sabotrax/agon-retro-case/pic/presentation/ac15-chamfered_egde.jpg

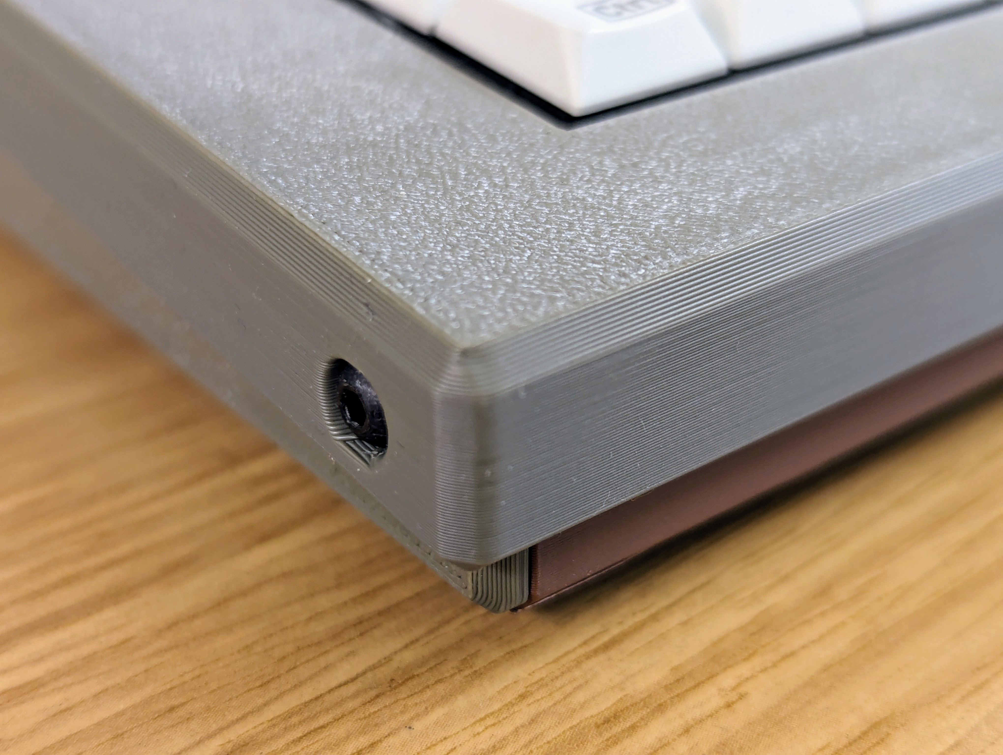
pic/presentation/ac15-chamfered_egde.jpg
