sabotrax/agon-retro-case/pic/presentation/ac15-expansion_ports-2.jpg

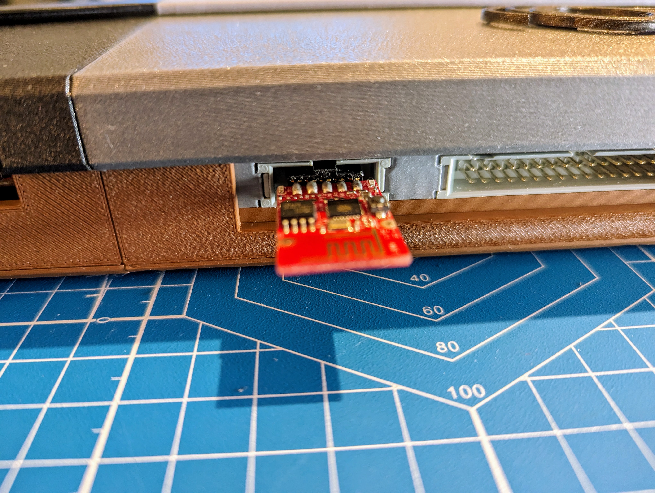
pic/presentation/ac15-expansion_ports-2.jpg
