sabotrax/agon-retro-case/pic/presentation/ac15-feet.jpg

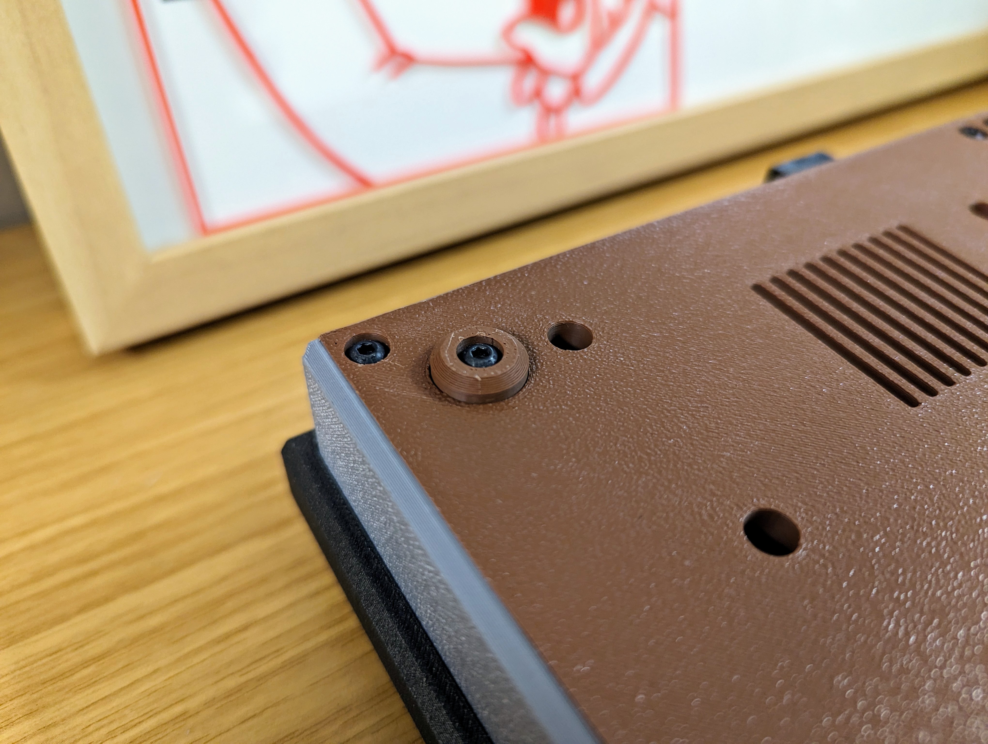
pic/presentation/ac15-feet.jpg
