sabotrax/agon-retro-case/pic/presentation/ac15-top.jpg

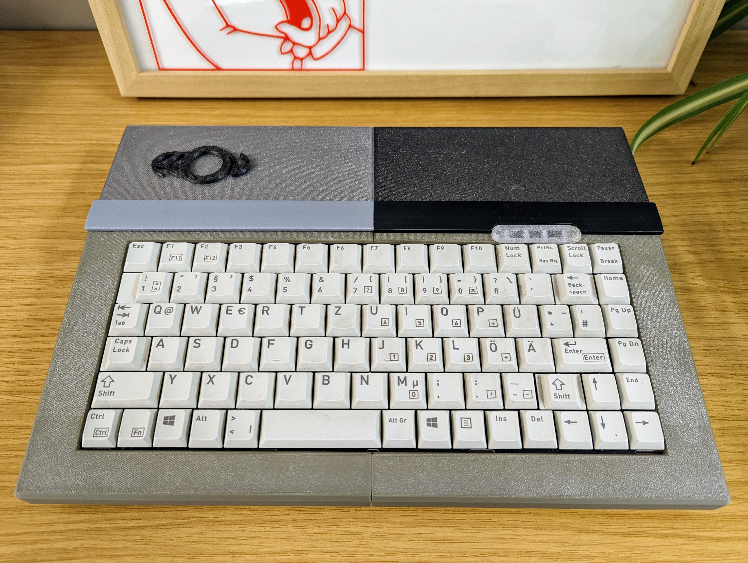
pic/presentation/ac15-top.jpg
