sabotrax/agon-retro-case/pic/prototype/agon.jpg

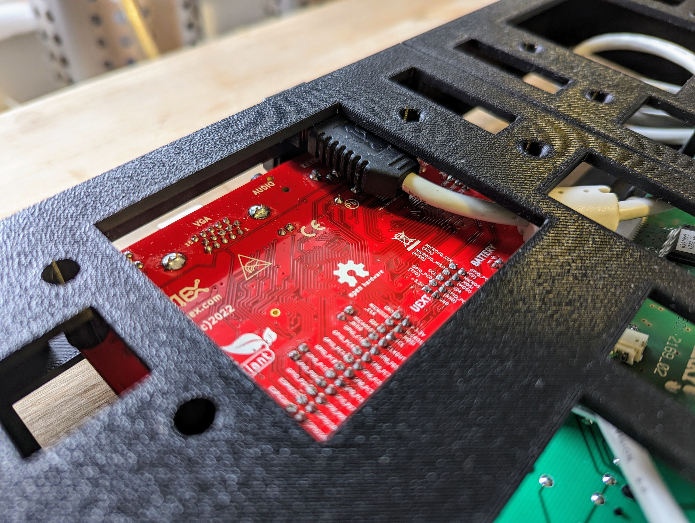
pic/prototype/agon.jpg
