sabotrax/agon-retro-case/pic/prototype/back_left-2.jpg

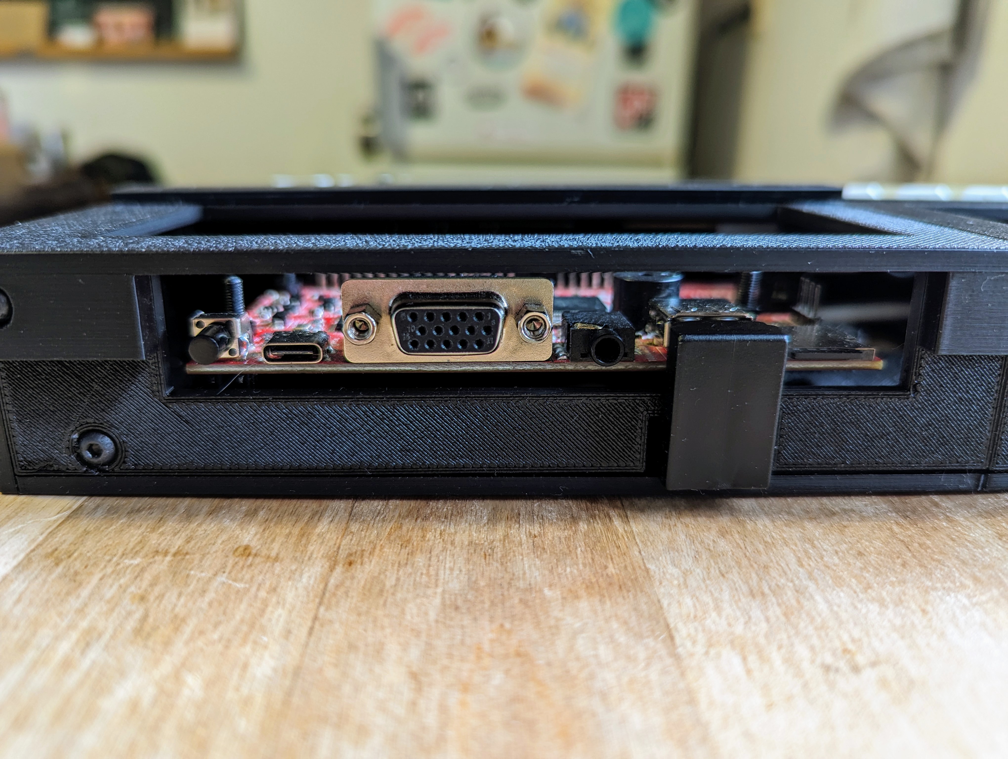
pic/prototype/back_left-2.jpg
