sabotrax/agon-retro-case/pic/prototype/back_left.jpg

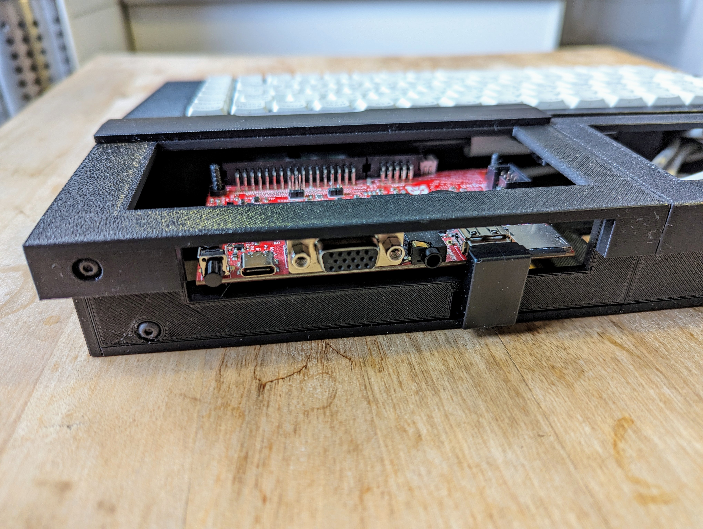
pic/prototype/back_left.jpg
