sabotrax/agon-retro-case/pic/prototype/daughterboard.jpg

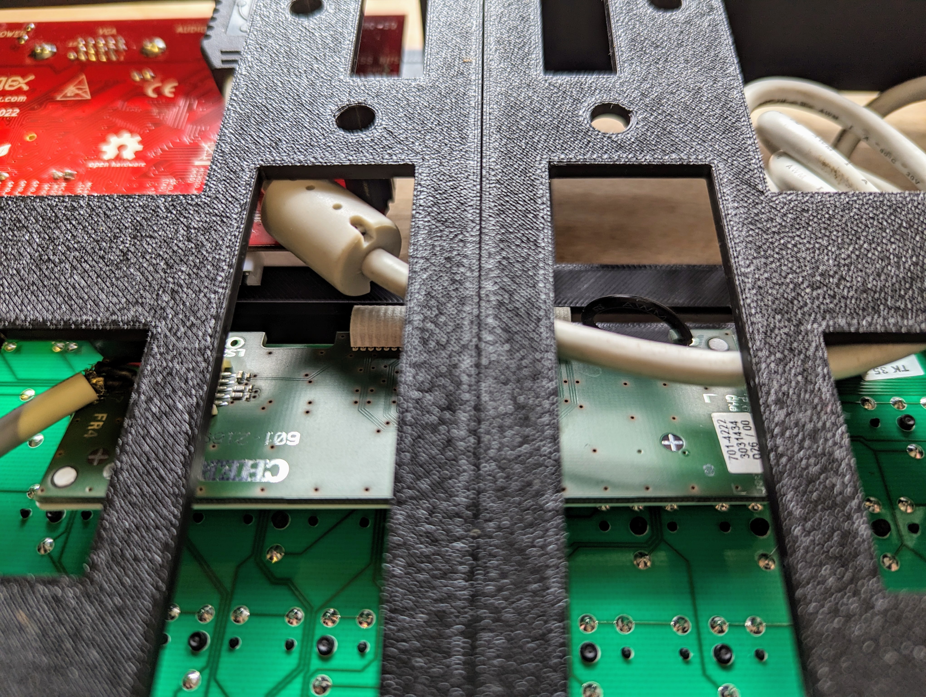
pic/prototype/daughterboard.jpg
