sabotrax/agon-retro-case/pic/prototype/expansion_ports.jpg

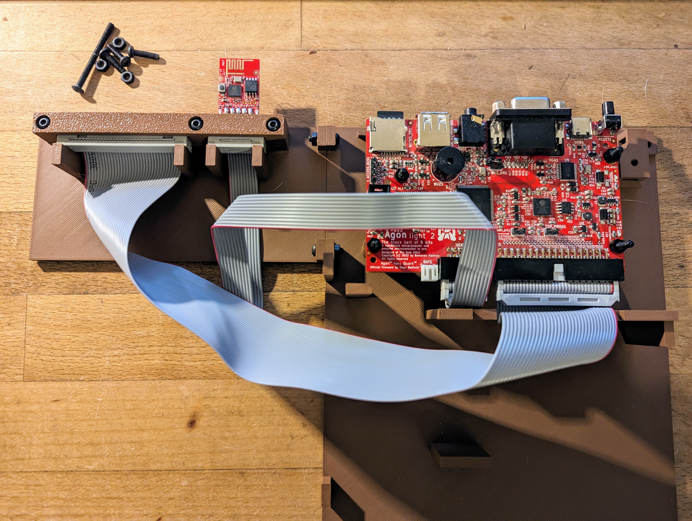
pic/prototype/expansion_ports.jpg
