sabotrax/agon-retro-case/pic/prototype/side_left.jpg

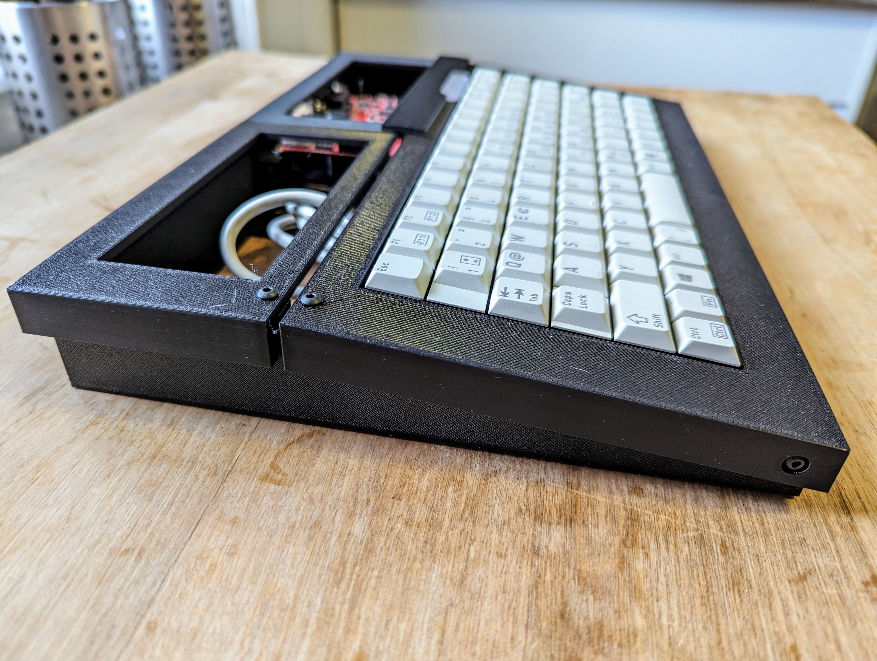
pic/prototype/side_left.jpg
