sabotrax/agon-retro-case/pic/prototype/top.jpg

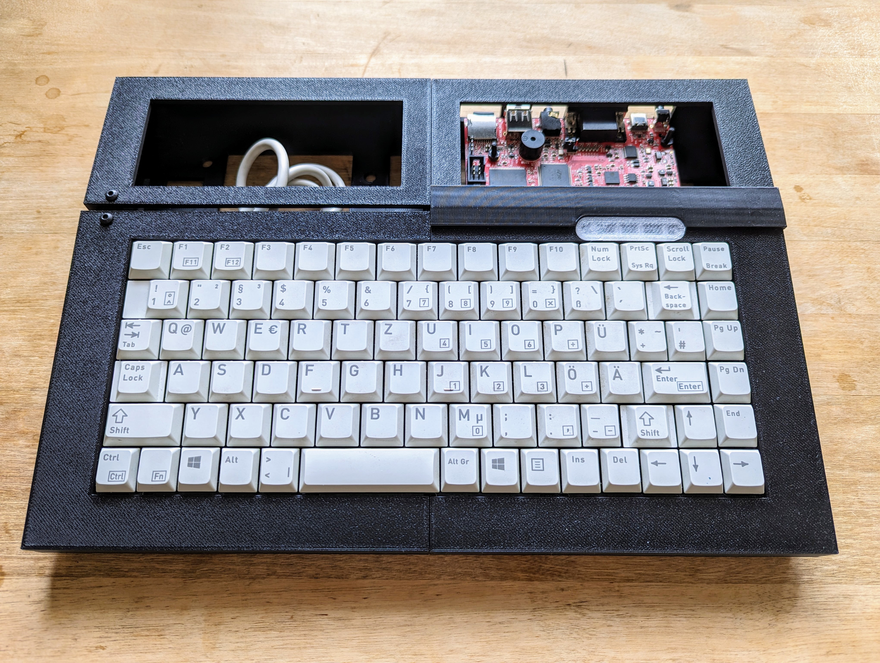
pic/prototype/top.jpg
