sabotrax/agon-retro-case/pic/prototype/top_right-2.jpg

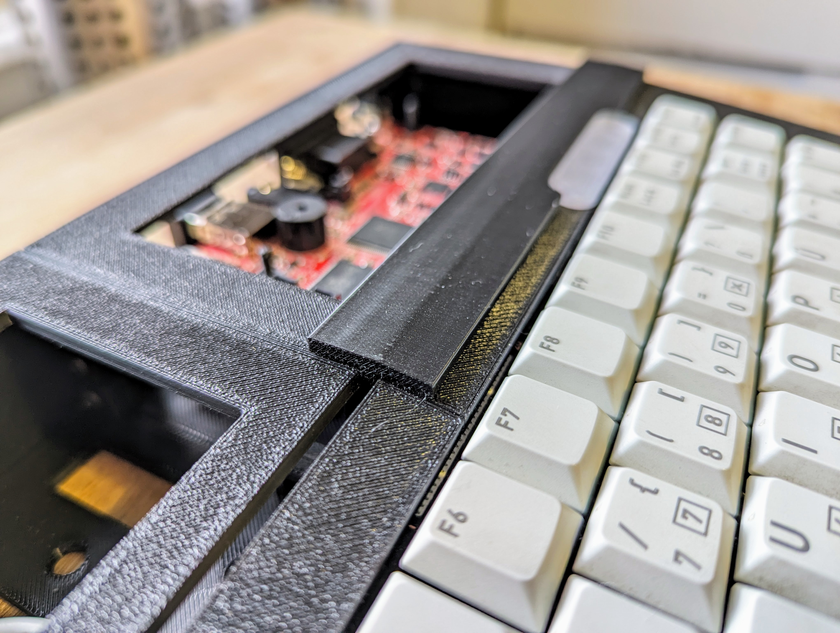
pic/prototype/top_right-2.jpg
