sabotrax/agon-retro-case/pic/prototype/top_right.jpg

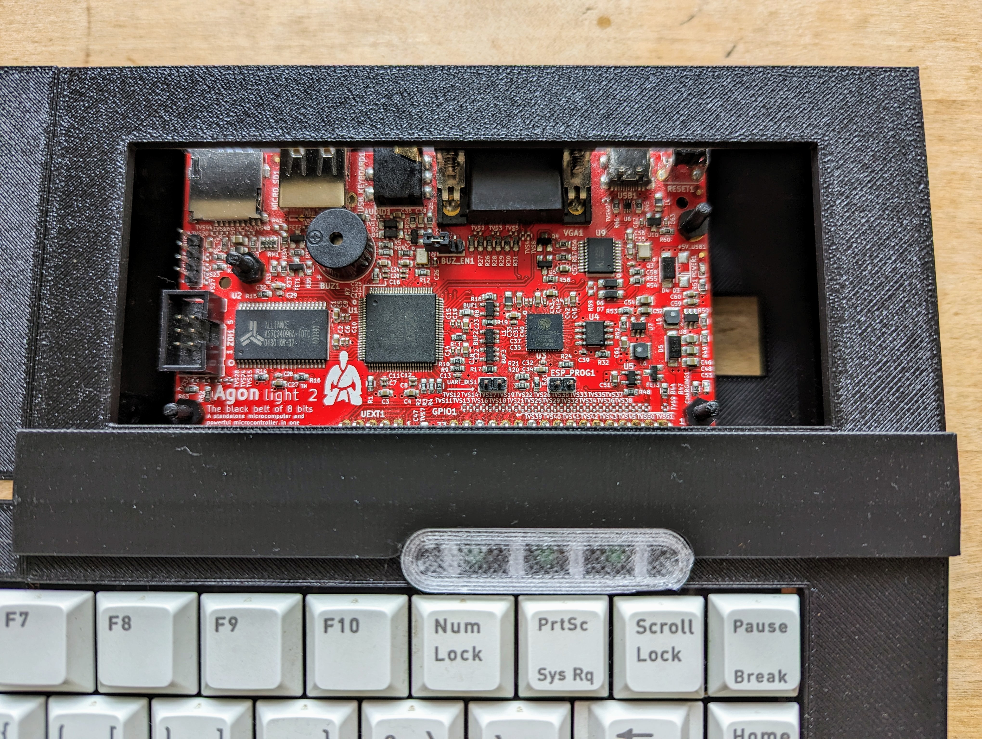
pic/prototype/top_right.jpg
