sabotrax/agon-retro-case/stl/ac_blind-left.stl

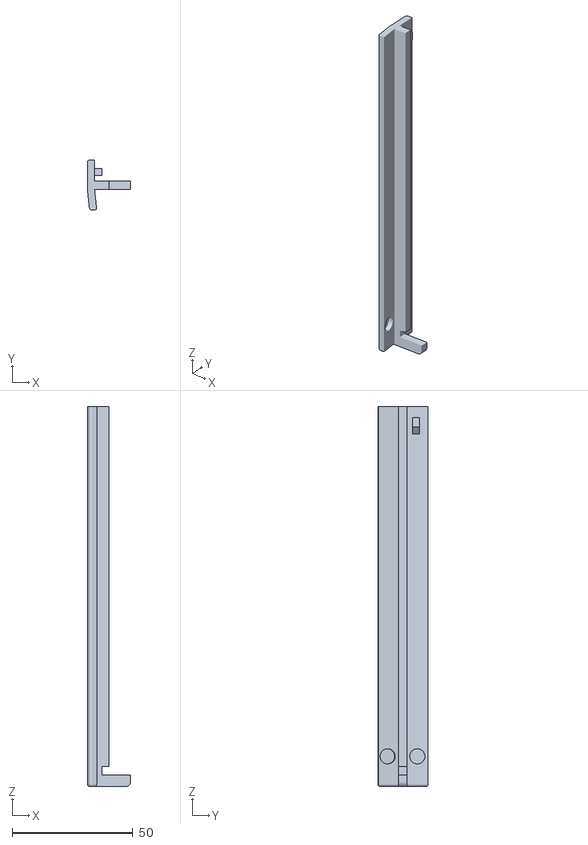
[picture p33: CAD file, 2024-01-17]
stl/ac_blind-left.stl
18.0 x 20.8 x 157.5
