sabotrax/agon-retro-case/stl/ac_isolator.stl

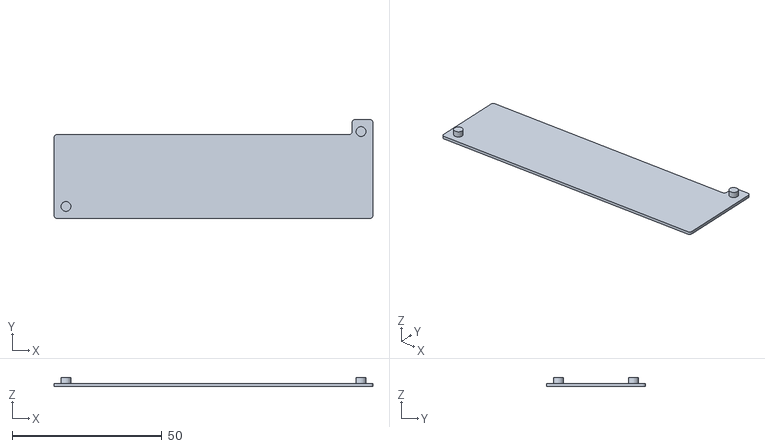
[picture p34: CAD file, 2024-01-12]
stl/ac_isolator.stl
106.5 x 33.0 x 3.00
