sabotrax/agon-retro-case/pic/assembly/ac15-ass01-undercarriage-1.jpg

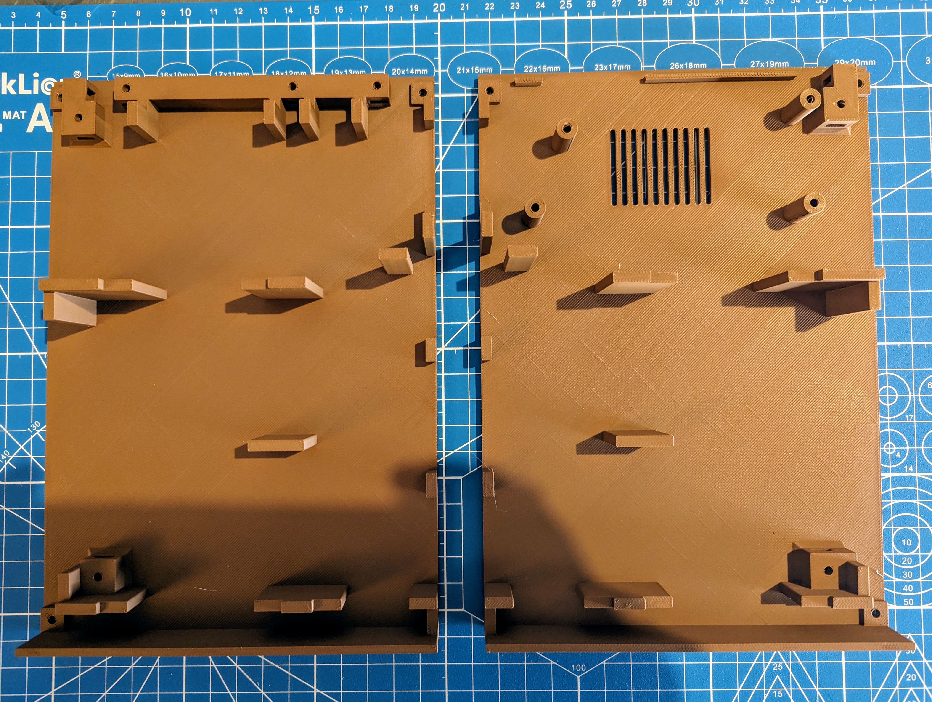
pic/assembly/ac15-ass01-undercarriage-1.jpg
