sabotrax/agon-retro-case/pic/assembly/ac15-ass02-undercarriage-2.jpg

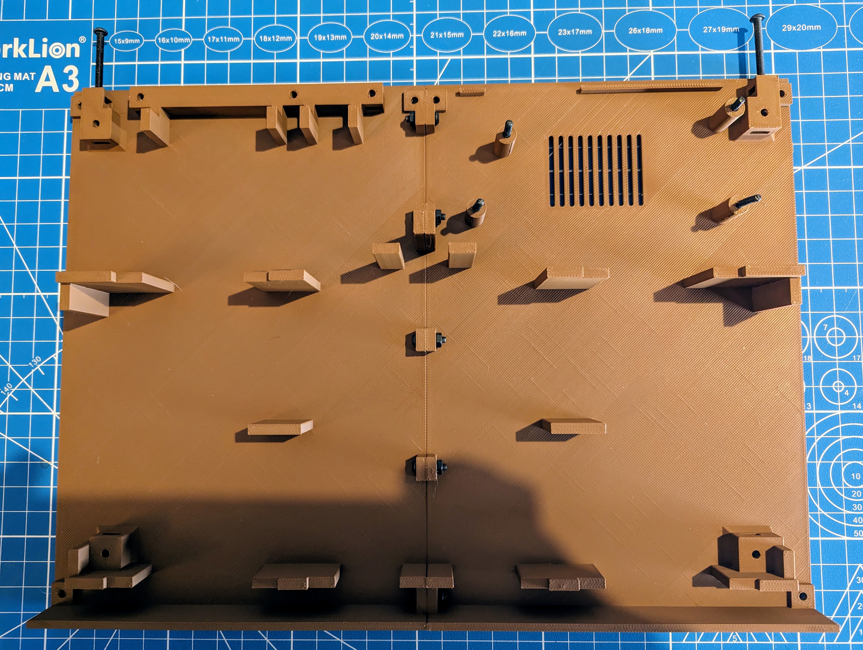
pic/assembly/ac15-ass02-undercarriage-2.jpg
