sabotrax/agon-retro-case/pic/assembly/ac15-ass03-side_walls-1.jpg

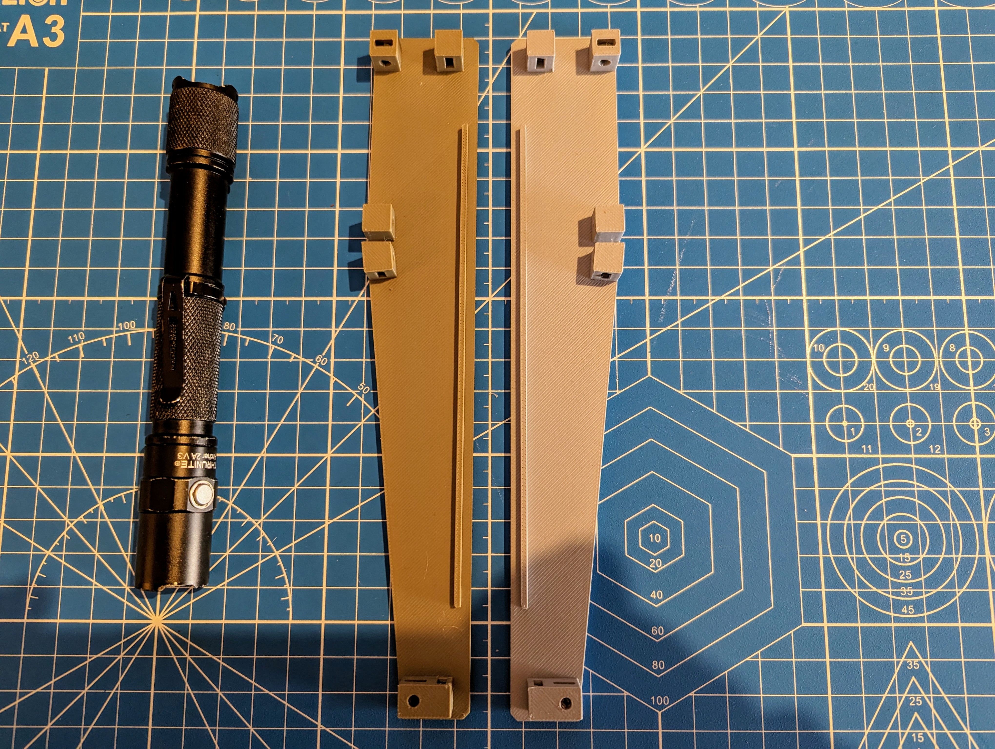
pic/assembly/ac15-ass03-side_walls-1.jpg
