sabotrax/agon-retro-case/pic/assembly/ac15-ass04-side_walls-2.jpg

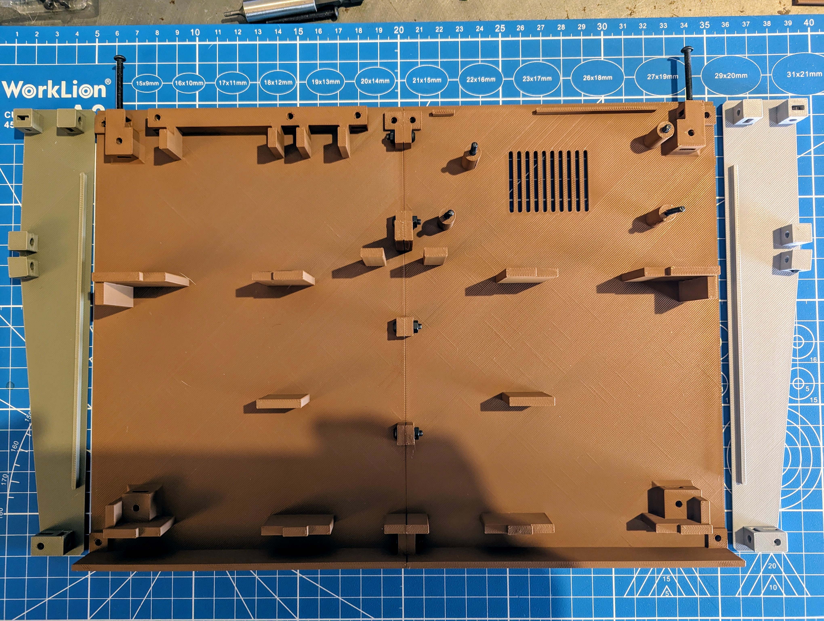
pic/assembly/ac15-ass04-side_walls-2.jpg
