sabotrax/agon-retro-case/pic/assembly/ac15-ass05-side_walls-3.jpg

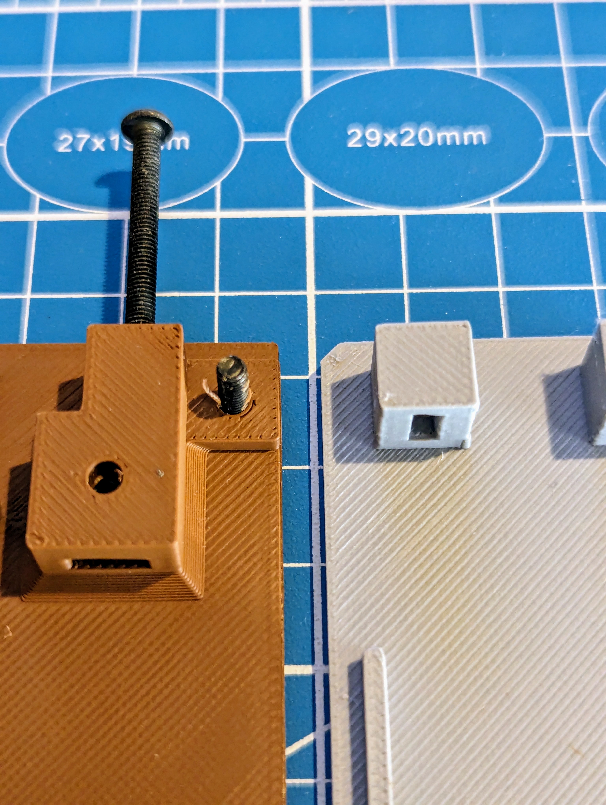
pic/assembly/ac15-ass05-side_walls-3.jpg
