sabotrax/agon-retro-case/pic/assembly/ac15-ass06-side_walls-4.jpg

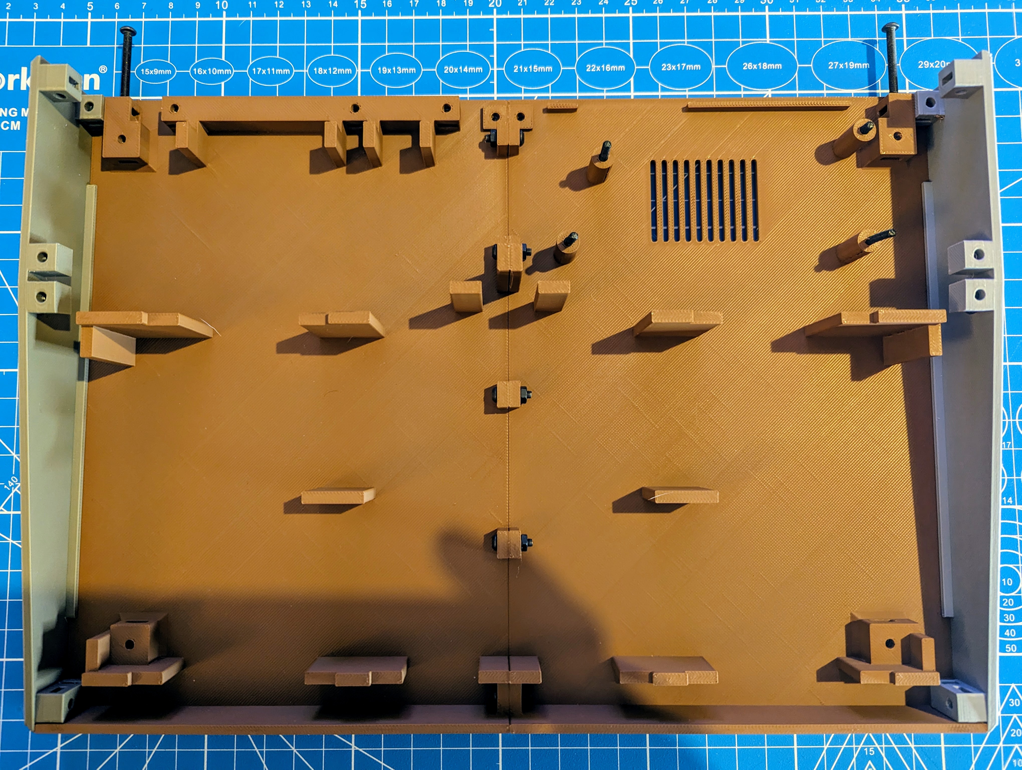
pic/assembly/ac15-ass06-side_walls-4.jpg
