sabotrax/agon-retro-case/pic/assembly/ac15-ass07-agon_expports-1.jpg

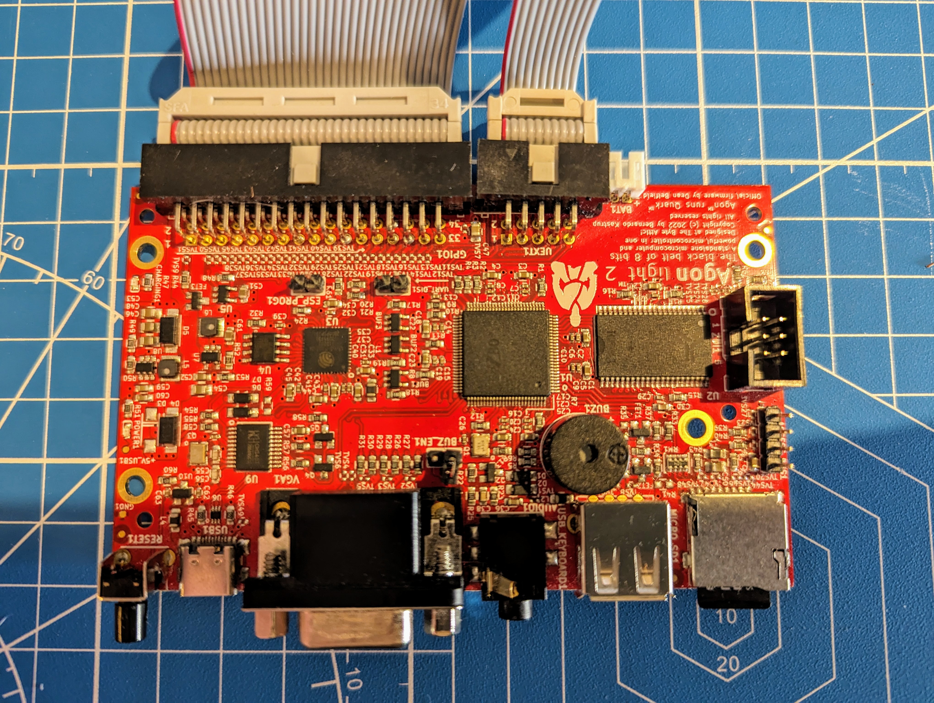
pic/assembly/ac15-ass07-agon_expports-1.jpg
