sabotrax/agon-retro-case/pic/assembly/ac15-ass08-agon_expports-2.jpg

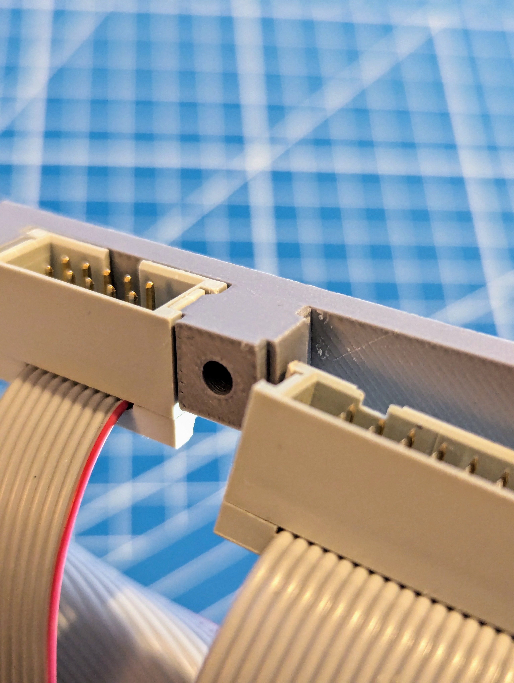
pic/assembly/ac15-ass08-agon_expports-2.jpg
