sabotrax/agon-retro-case/pic/assembly/ac15-ass09-agon_expports-3.jpg

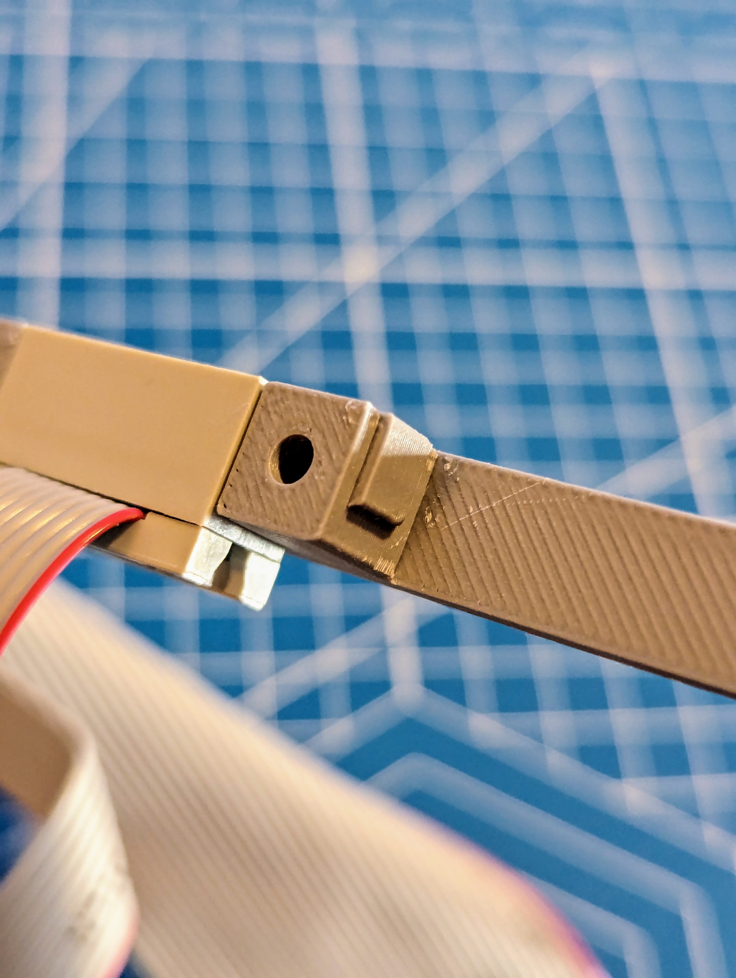
pic/assembly/ac15-ass09-agon_expports-3.jpg
