sabotrax/agon-retro-case/pic/assembly/ac15-ass10-agon_expports-4.jpg

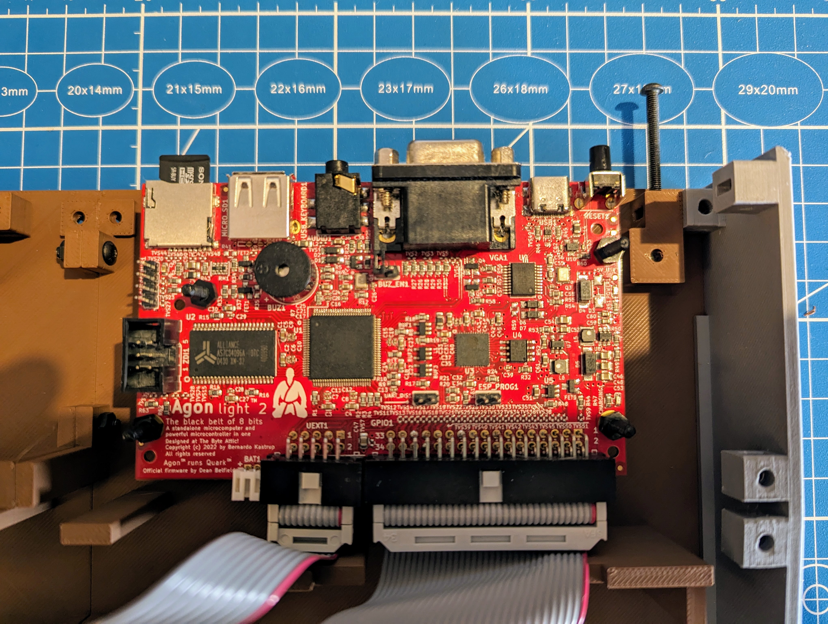
pic/assembly/ac15-ass10-agon_expports-4.jpg
