sabotrax/agon-retro-case/pic/assembly/ac15-ass11-agon_expports-5.jpg

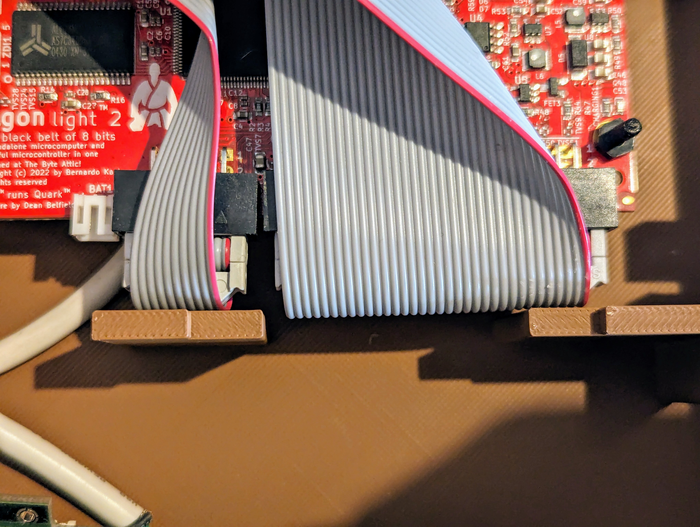
pic/assembly/ac15-ass11-agon_expports-5.jpg
