sabotrax/agon-retro-case/pic/assembly/ac15-ass12-agon_expports-6.jpg

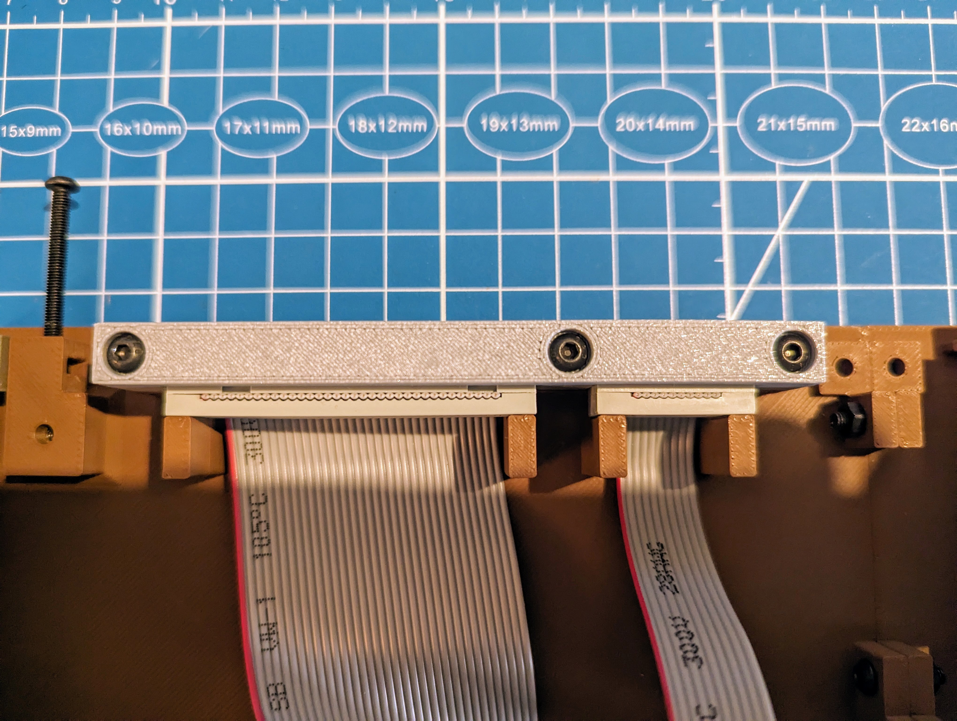
pic/assembly/ac15-ass12-agon_expports-6.jpg
