sabotrax/agon-retro-case/pic/assembly/ac15-ass13-agon_expports-7.jpg

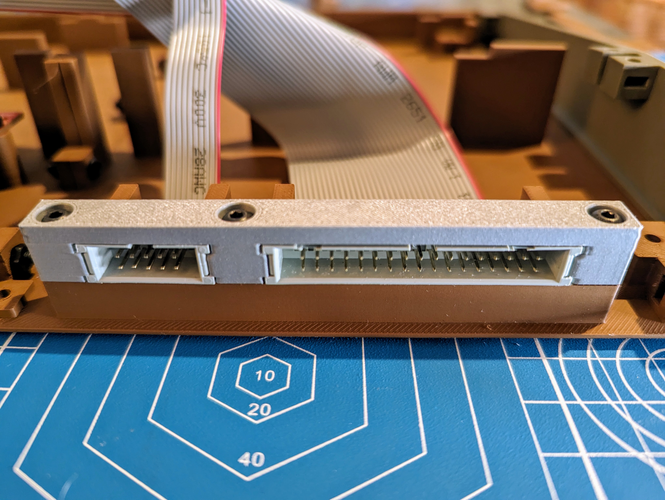
pic/assembly/ac15-ass13-agon_expports-7.jpg
