sabotrax/agon-retro-case/pic/assembly/ac15-ass15-agon_expports-9.jpg

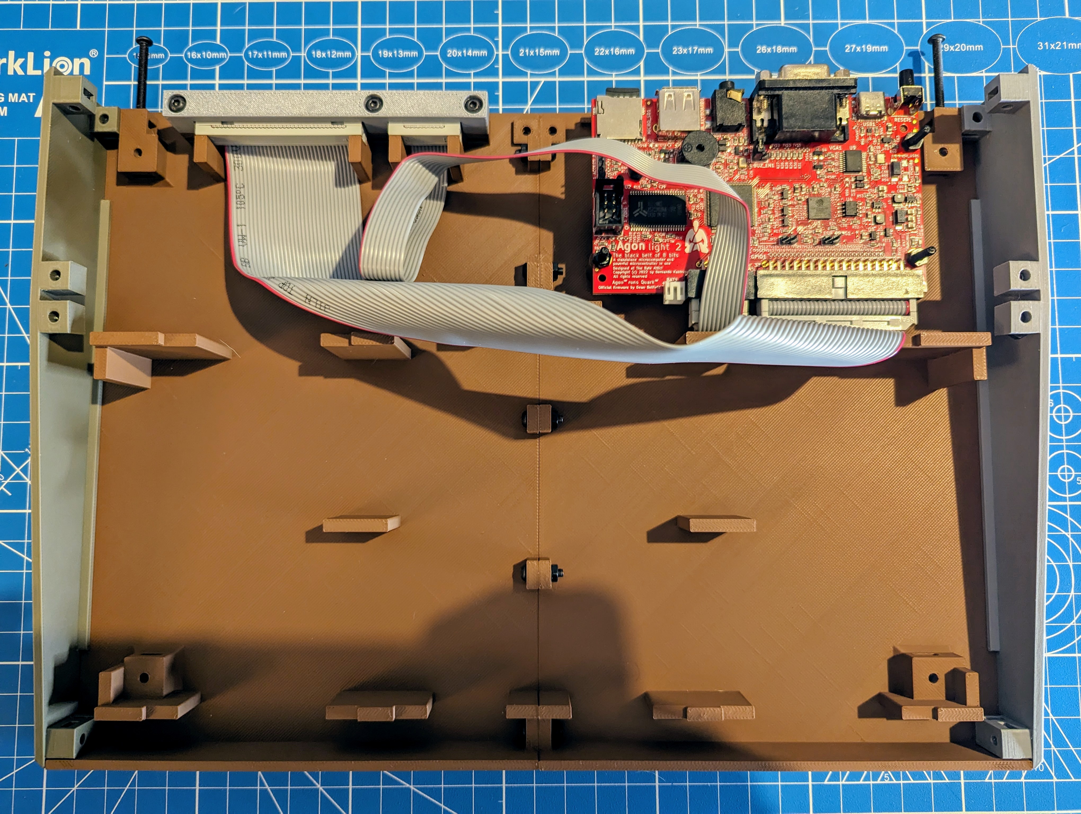
pic/assembly/ac15-ass15-agon_expports-9.jpg
