sabotrax/agon-retro-case/pic/assembly/ac15-ass17-back_wall-1.jpg

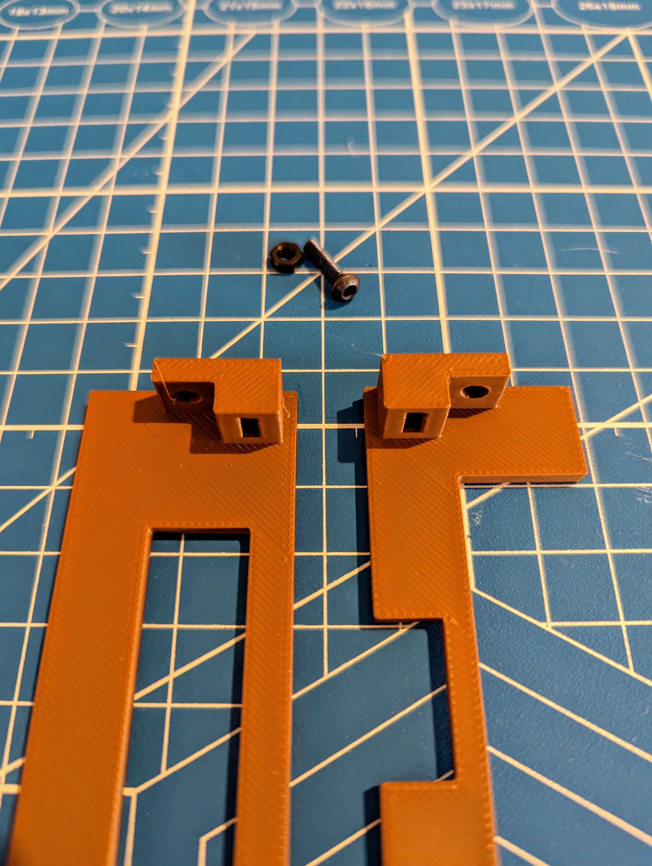
pic/assembly/ac15-ass17-back_wall-1.jpg
