sabotrax/agon-retro-case/pic/assembly/ac15-ass18-back_wall-2.jpg

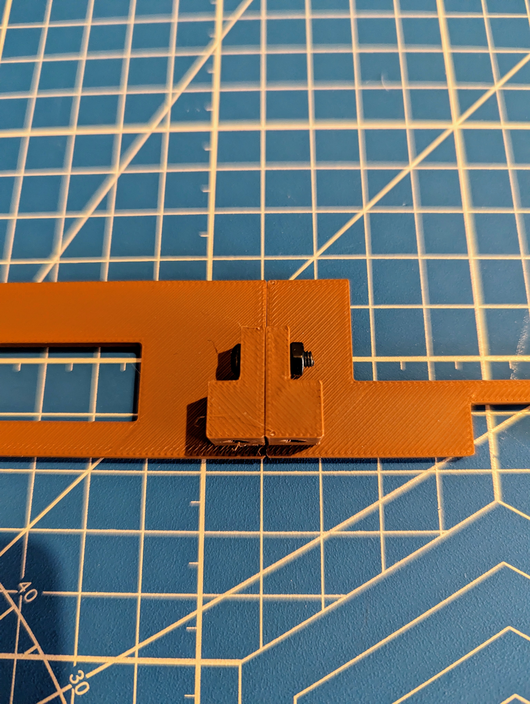
pic/assembly/ac15-ass18-back_wall-2.jpg
