sabotrax/agon-retro-case/pic/assembly/ac15-ass21-back_wall-5.jpg

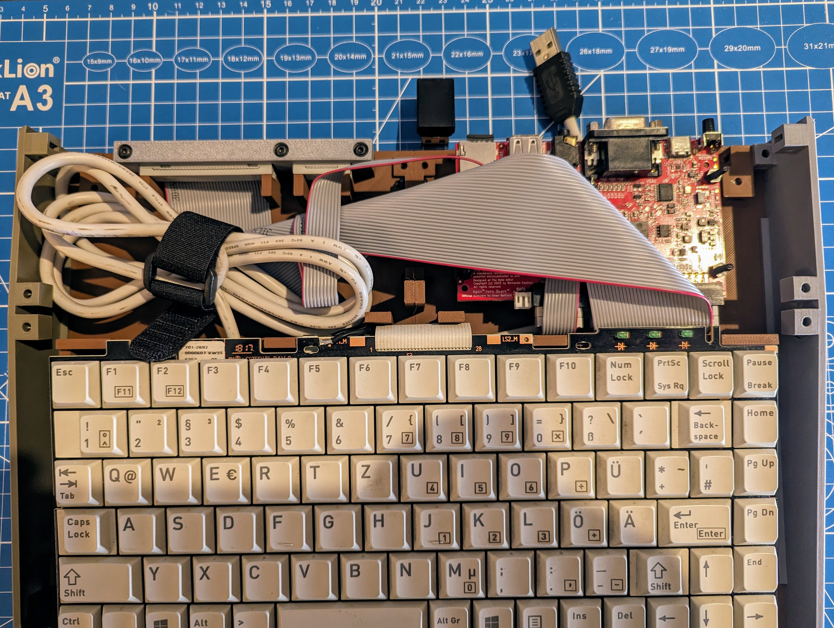
pic/assembly/ac15-ass21-back_wall-5.jpg
