sabotrax/agon-retro-case/pic/assembly/ac15-ass23-back_wall-7.jpg

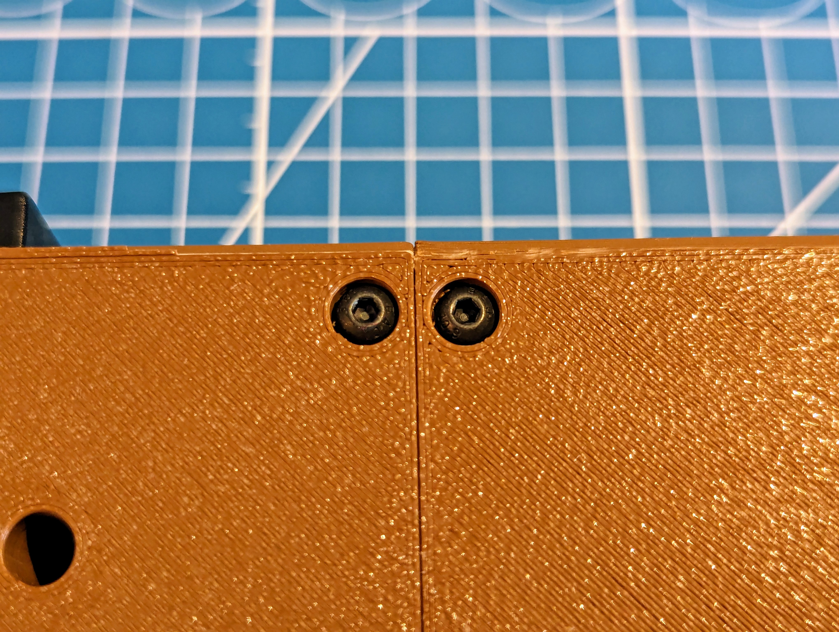
pic/assembly/ac15-ass23-back_wall-7.jpg
