sabotrax/agon-retro-case/pic/assembly/ac15-ass26-top_cover-3.jpg

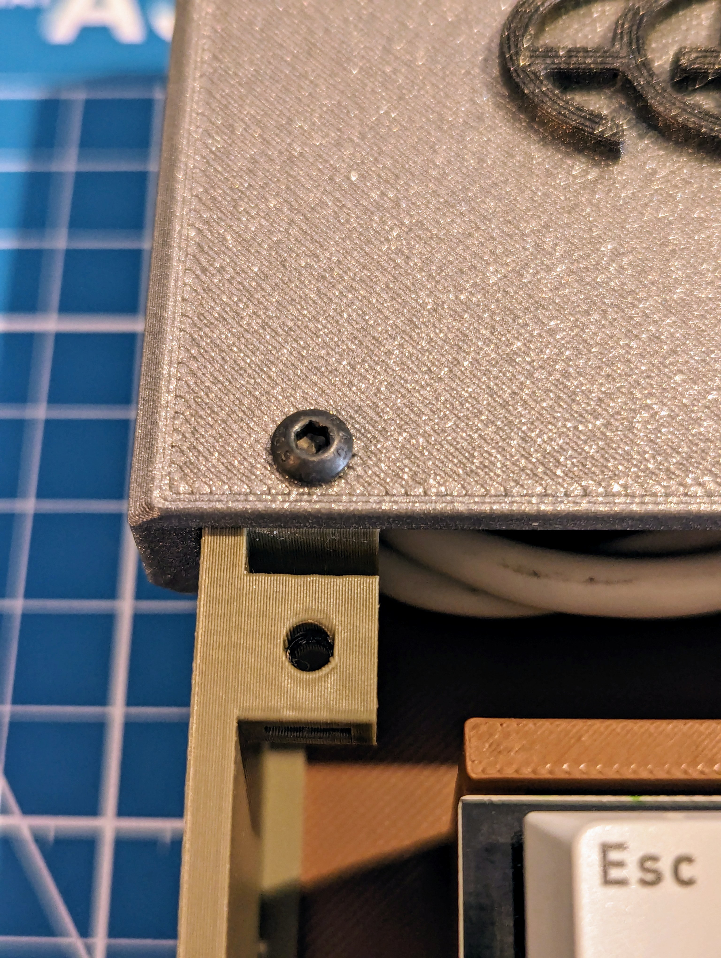
pic/assembly/ac15-ass26-top_cover-3.jpg
