sabotrax/agon-retro-case/pic/assembly/ac15-ass27-top_cover-4.jpg

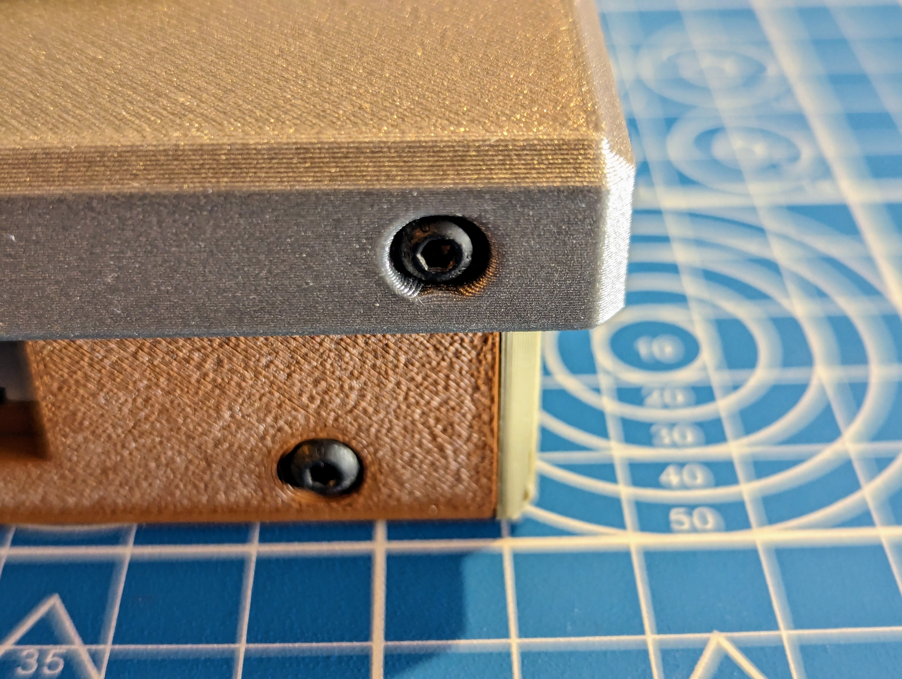
pic/assembly/ac15-ass27-top_cover-4.jpg
