sabotrax/agon-retro-case/pic/assembly/ac15-ass28-top_cover-5.jpg

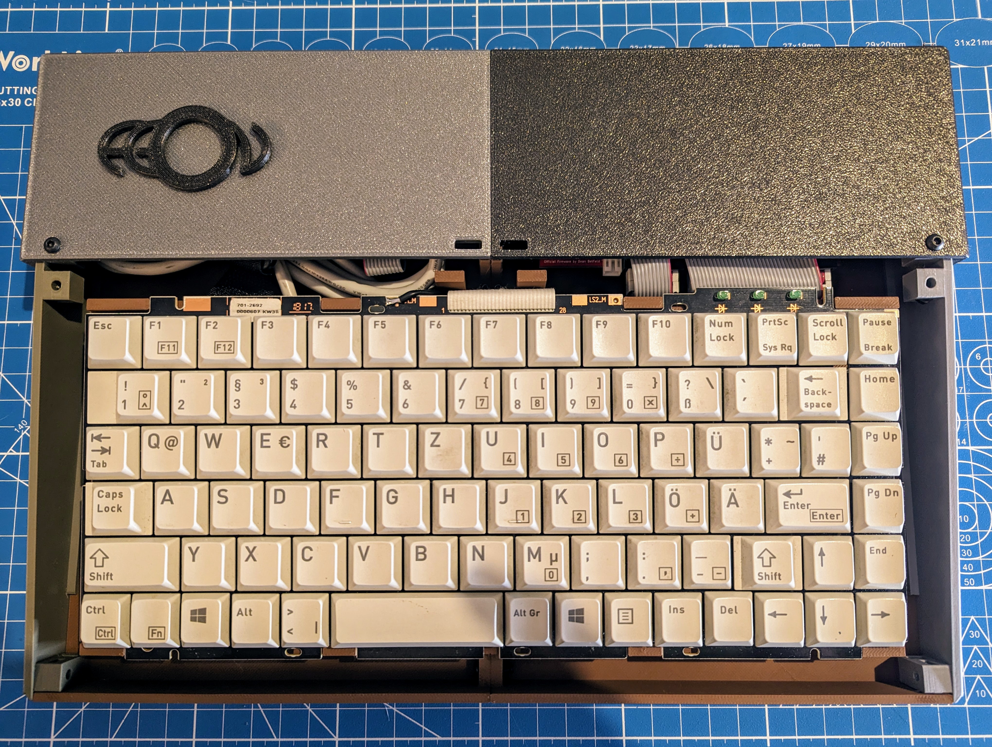
pic/assembly/ac15-ass28-top_cover-5.jpg
