sabotrax/agon-retro-case/pic/assembly/ac15-ass29-keyboard_frame-1.jpg

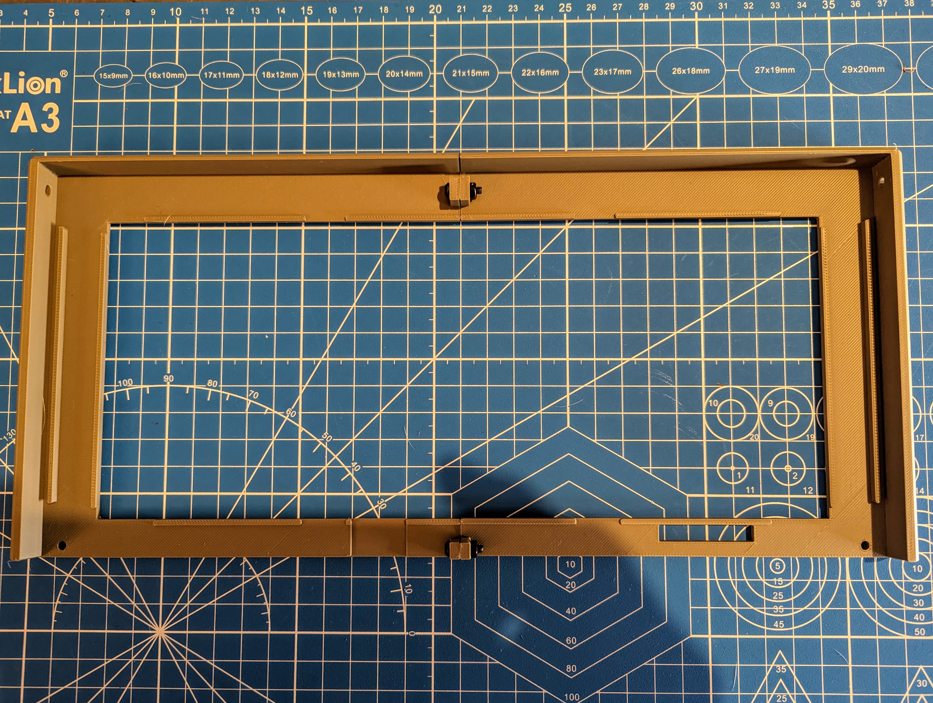
pic/assembly/ac15-ass29-keyboard_frame-1.jpg
