sabotrax/agon-retro-case/pic/assembly/ac15-ass30-keyboard_frame-2.jpg

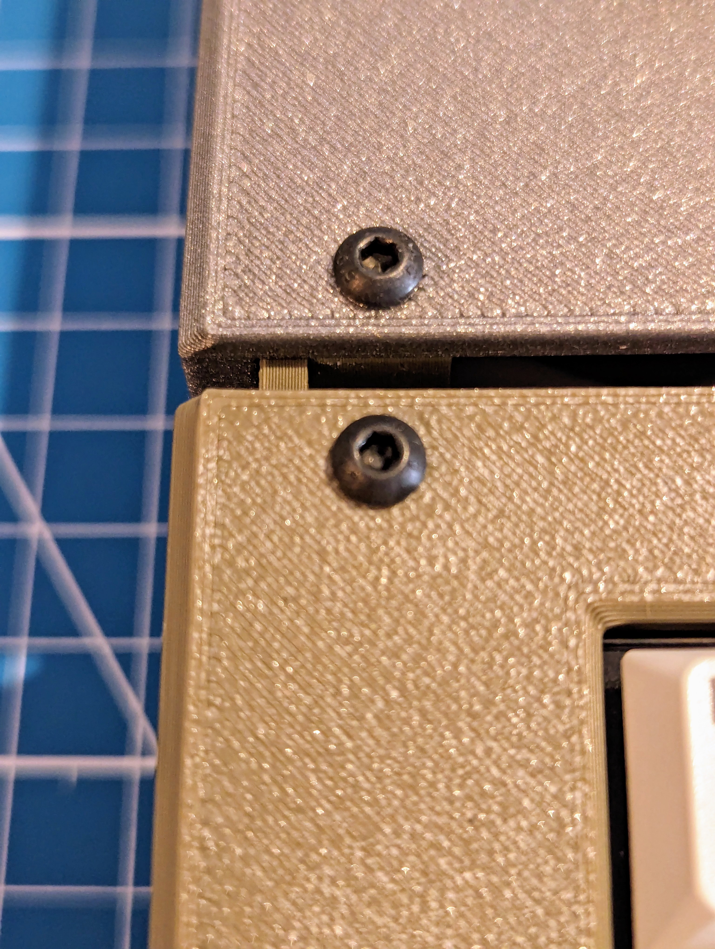
pic/assembly/ac15-ass30-keyboard_frame-2.jpg
