sabotrax/agon-retro-case/pic/assembly/ac15-ass31-keyboard_frame-3.jpg

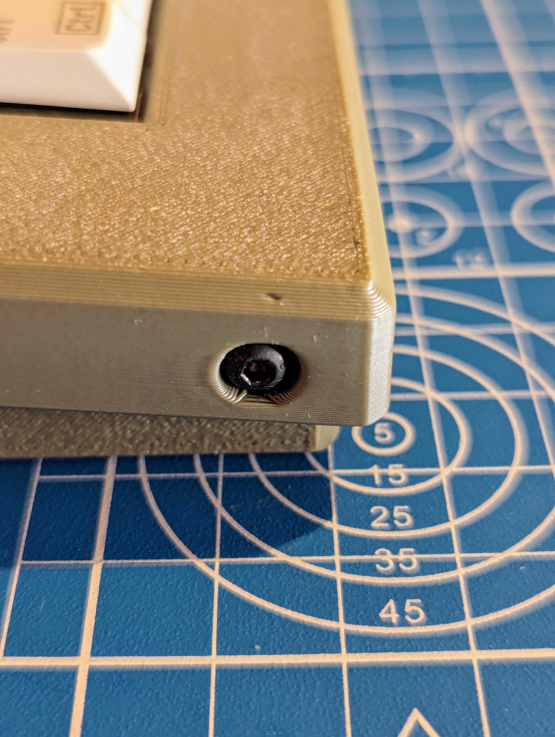
pic/assembly/ac15-ass31-keyboard_frame-3.jpg
