sabotrax/agon-retro-case/pic/assembly/ac15-ass35-blind-2.jpg

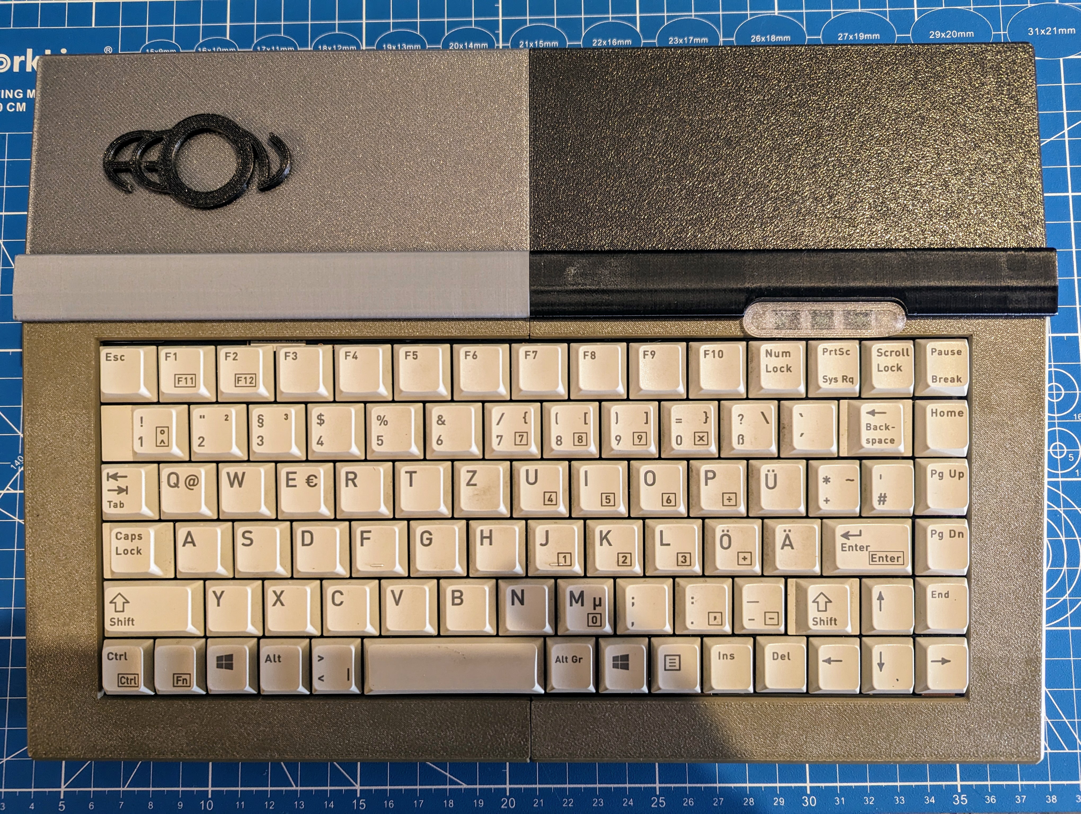
pic/assembly/ac15-ass35-blind-2.jpg
