sabotrax/agon-retro-case/pic/assembly/ac15-ass36-feet-1.jpg

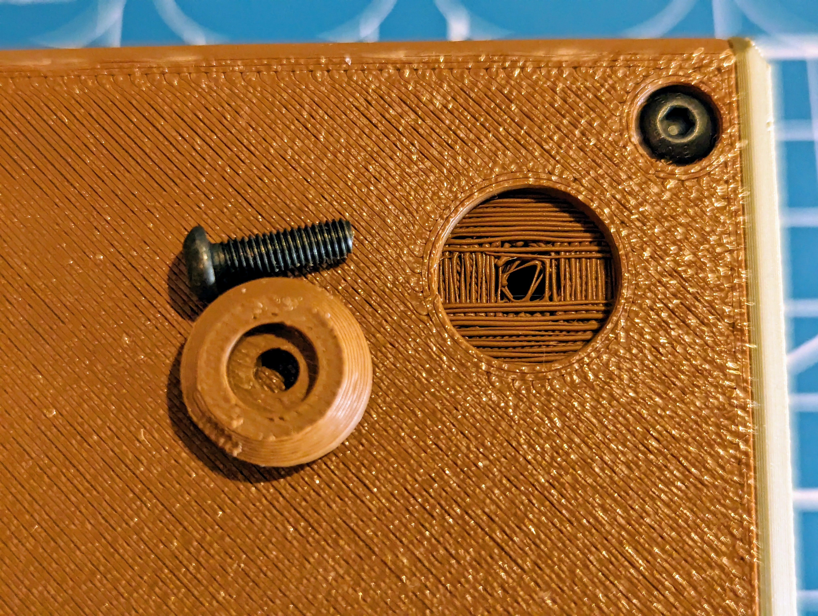
pic/assembly/ac15-ass36-feet-1.jpg
