sabotrax/agon-retro-case/pic/printables/ac_galaxy_black_and_clay-back_slot.jpg

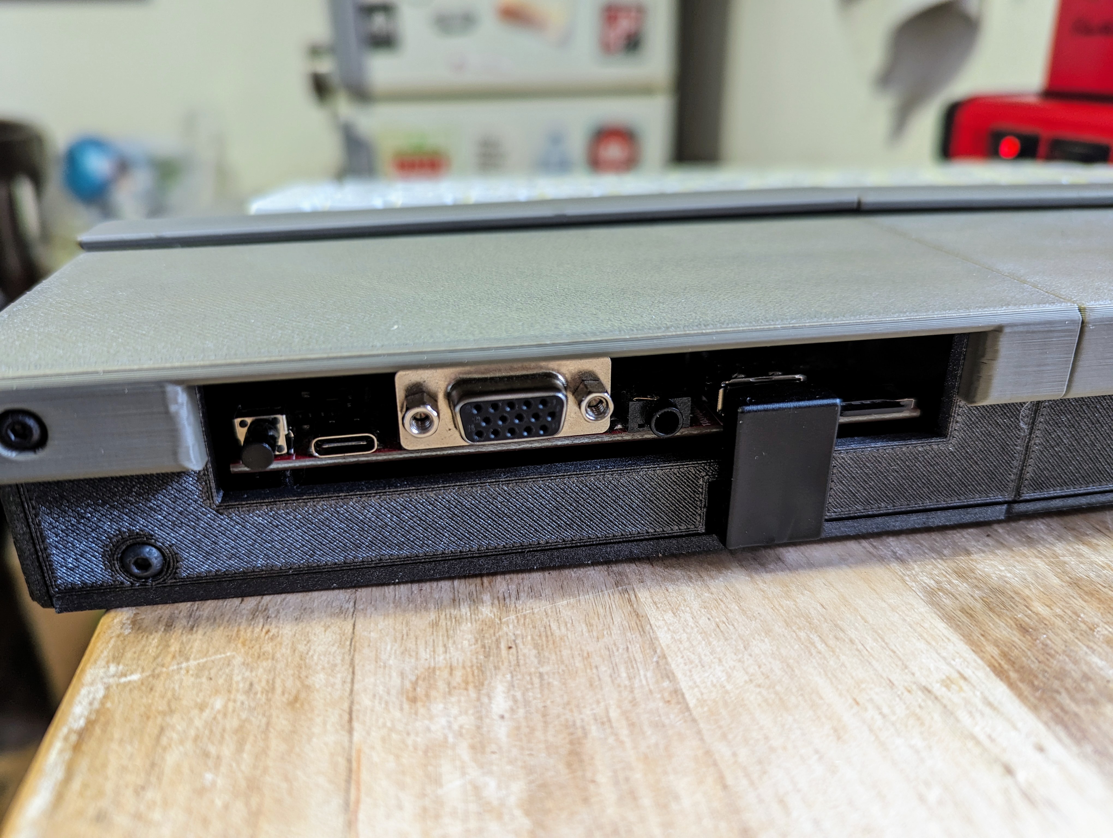
pic/printables/ac_galaxy_black_and_clay-back_slot.jpg
