sabotrax/agon-retro-case/pic/printables/ac_galaxy_black_and_clay-right.jpg

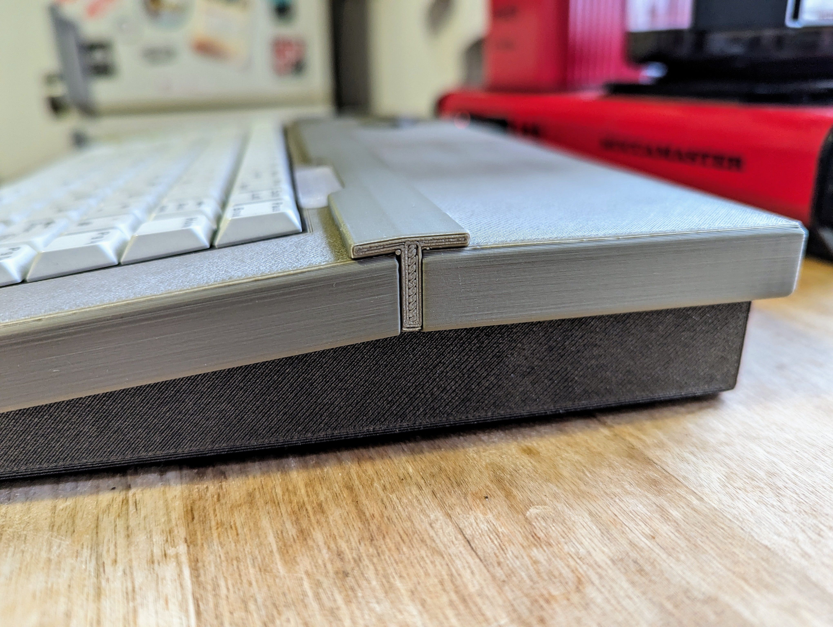
pic/printables/ac_galaxy_black_and_clay-right.jpg
