sabotrax/agon-retro-case/pic/printables/ac_galaxy_black_and_clay-top.jpg

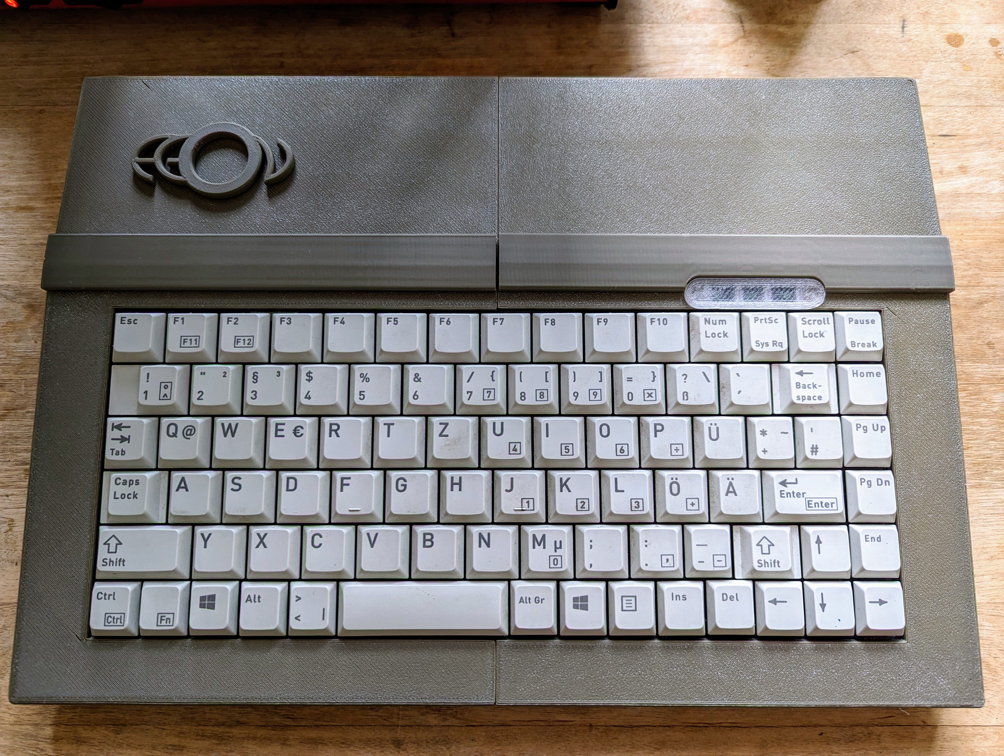
pic/printables/ac_galaxy_black_and_clay-top.jpg
