sabotrax/agon-retro-case/pic/printables/ac_in_good_company-2.jpg

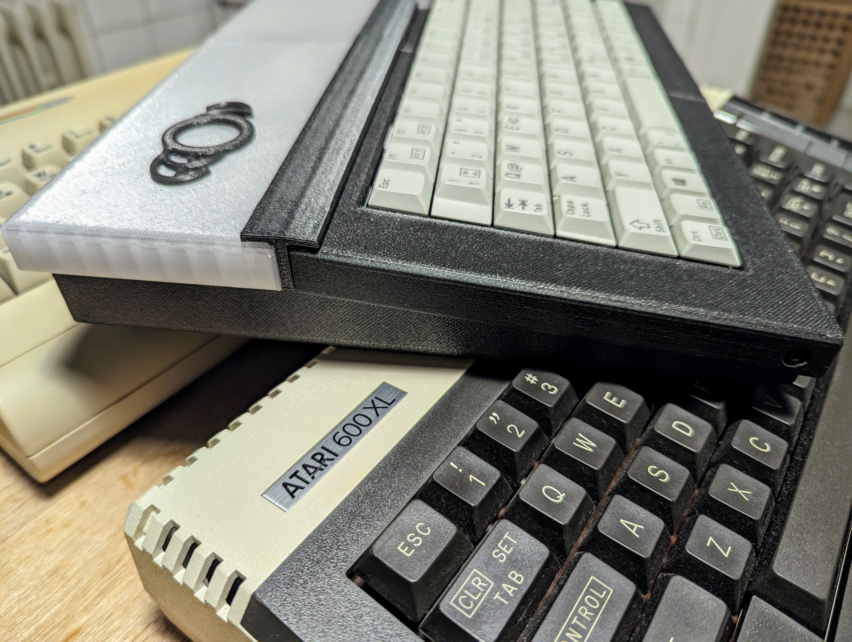
pic/printables/ac_in_good_company-2.jpg
