sabotrax/agon-retro-case/pic/printables/ac_in_good_company.jpg

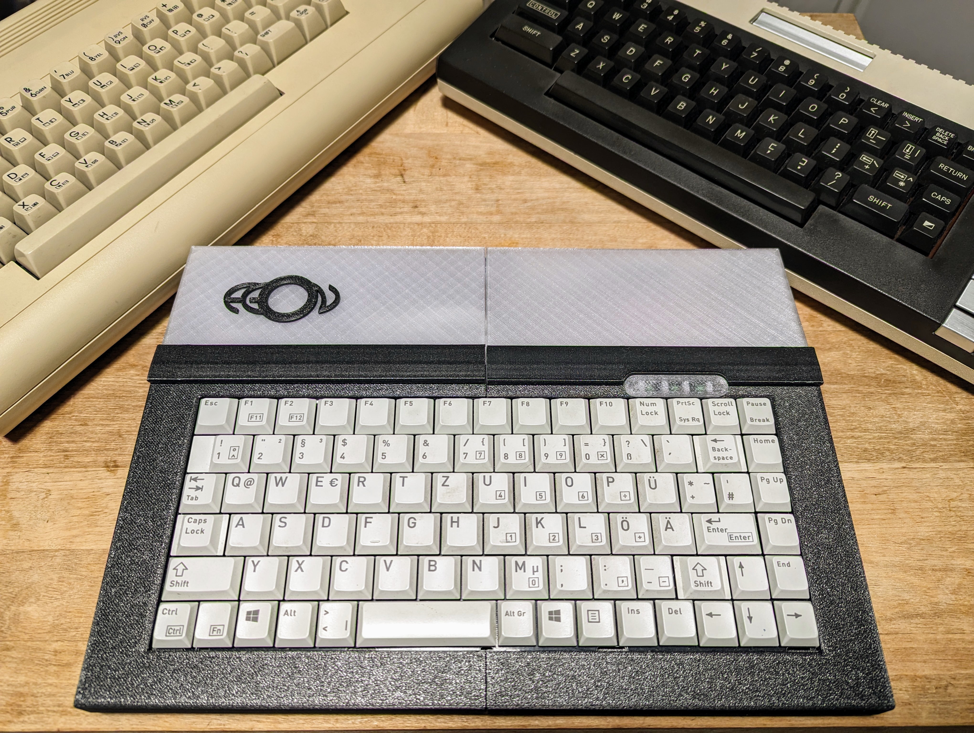
pic/printables/ac_in_good_company.jpg
