sabotrax/agon-retro-case/pic/assembly/ac15-ass16-qa_leads_rowdy_and_molly.jpg

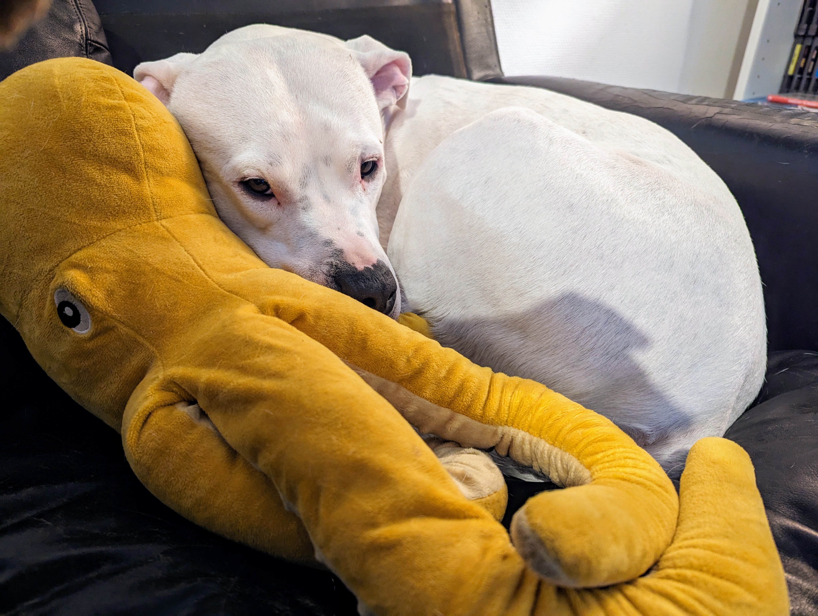
pic/assembly/ac15-ass16-qa_leads_rowdy_and_molly.jpg
